jabelpc/flyradar/docs/images/IMG_5898.jpeg

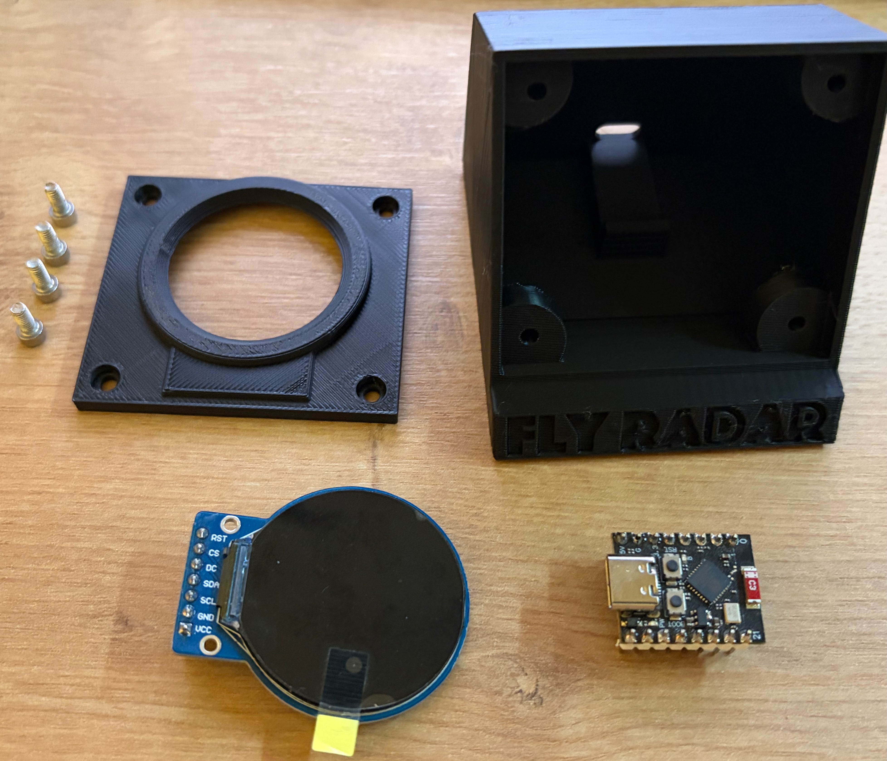
docs/images/IMG_5898.jpeg
