jabelpc/flyradar/docs/images/IMG_5900.jpeg

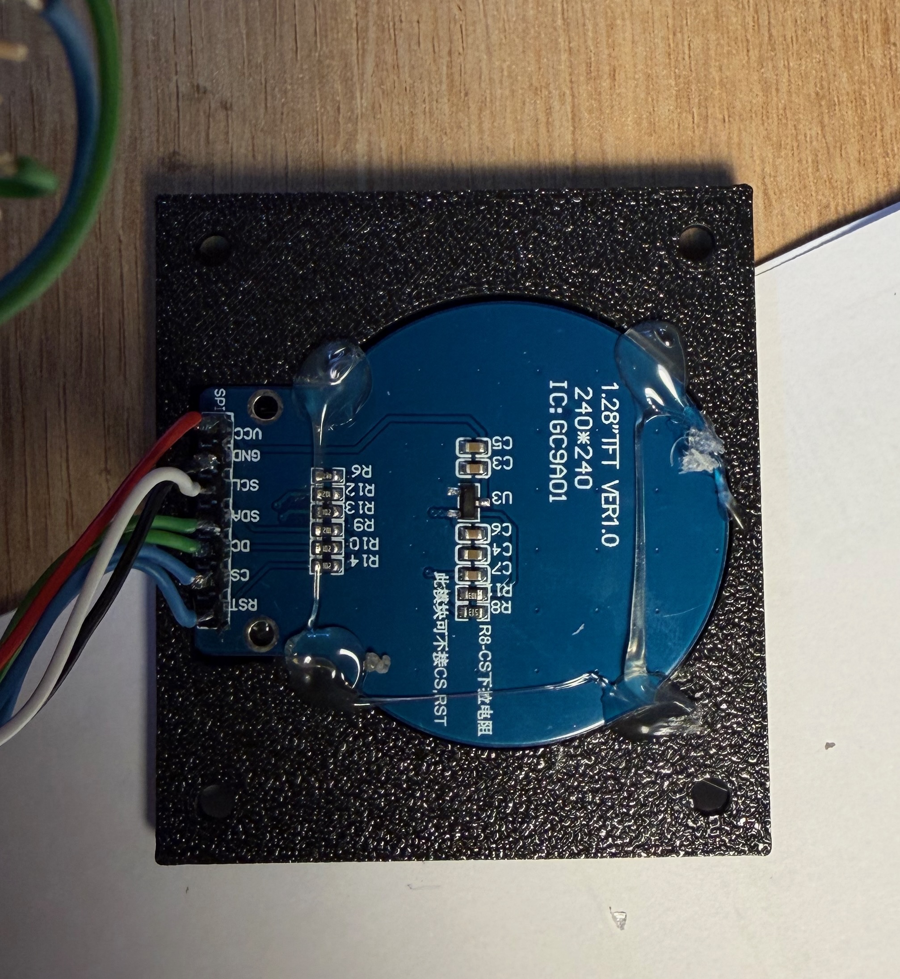
docs/images/IMG_5900.jpeg
