jabelpc/flyradar/docs/images/IMG_5901.jpeg

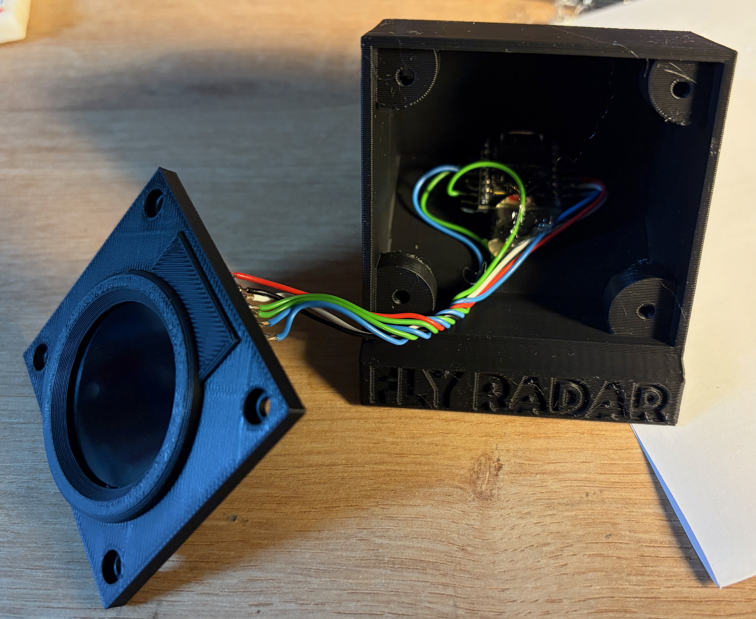
docs/images/IMG_5901.jpeg
